tkbletsc/Prusa3/printed_parts/output/Z_-Half_Coupler_v2.stl

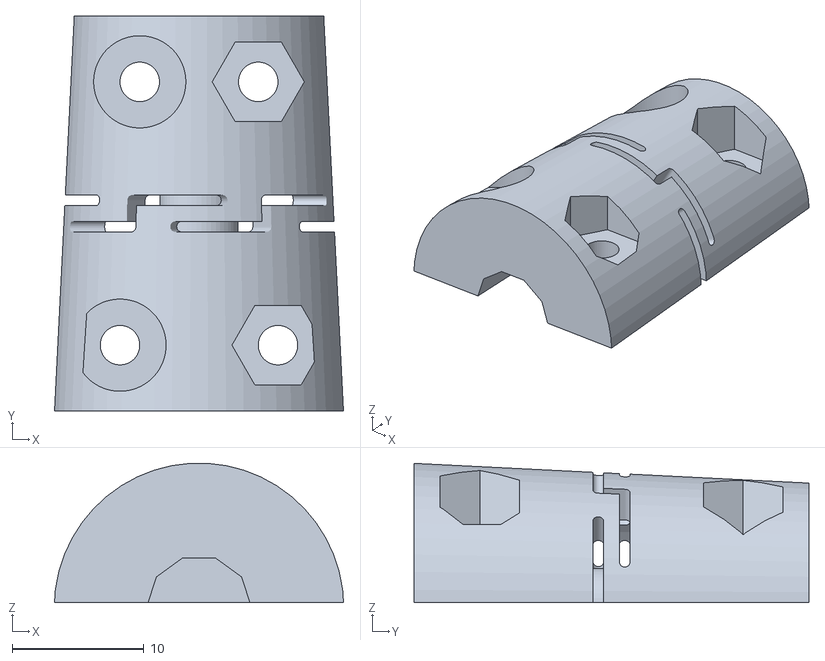
[picture p31: CAD file, 2015-11-13]
printed_parts/output/Z_-Half_Coupler_v2.stl
21.9 x 30.0 x 10.6
