tkbletsc/Prusa3/printed_parts/output/extras/foldingclamp.stl

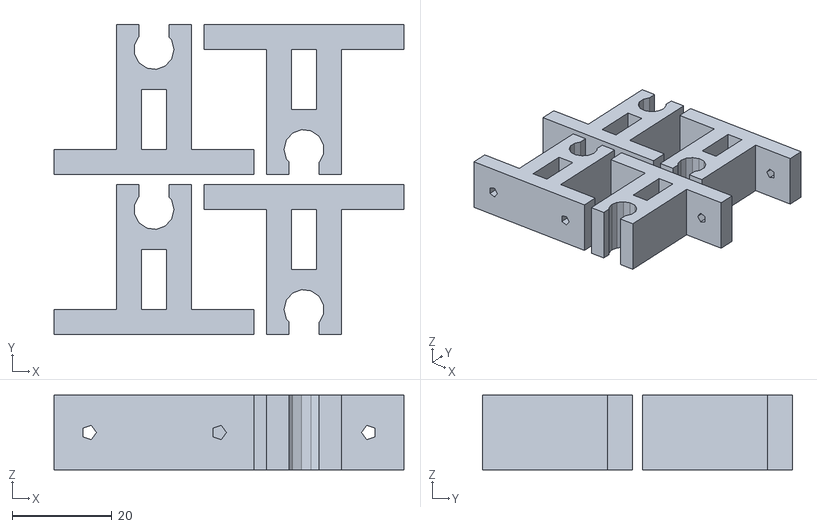
[picture p32: CAD file, 2015-11-13]
printed_parts/output/extras/foldingclamp.stl
70.0 x 62.0 x 15.0
