tkbletsc/Prusa3/printed_parts/output/Pulley_T-MXL-XL-HTD-GT2_N-tooth.stl

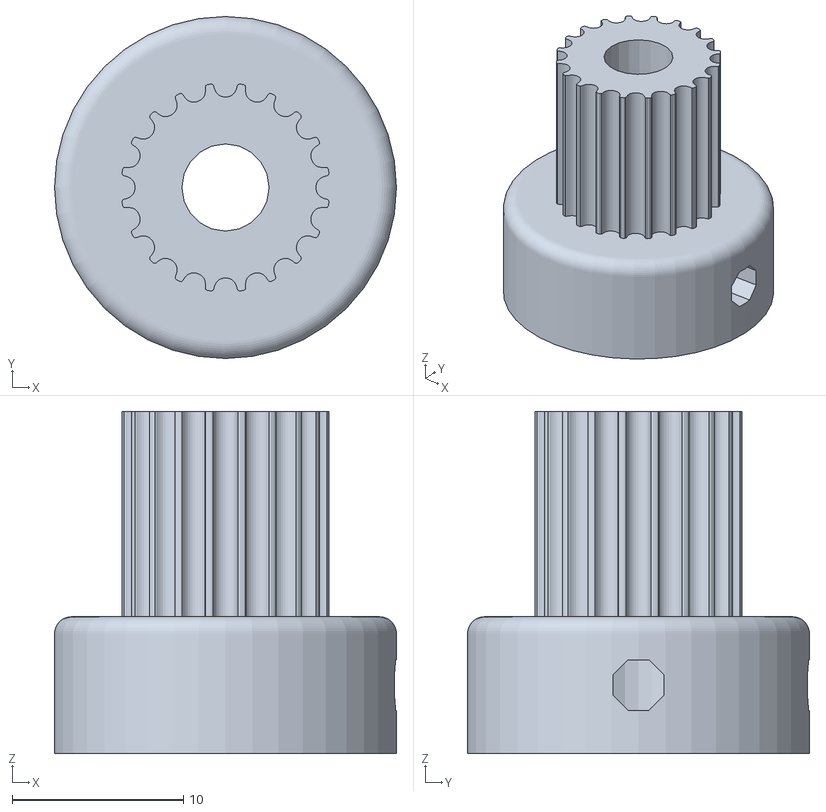
[picture p33: CAD file, 2015-11-13]
printed_parts/output/Pulley_T-MXL-XL-HTD-GT2_N-tooth.stl
20.0 x 20.0 x 20.0
