tkbletsc/Prusa3/printed_parts/output/extras/endstop-holder-extra.stl

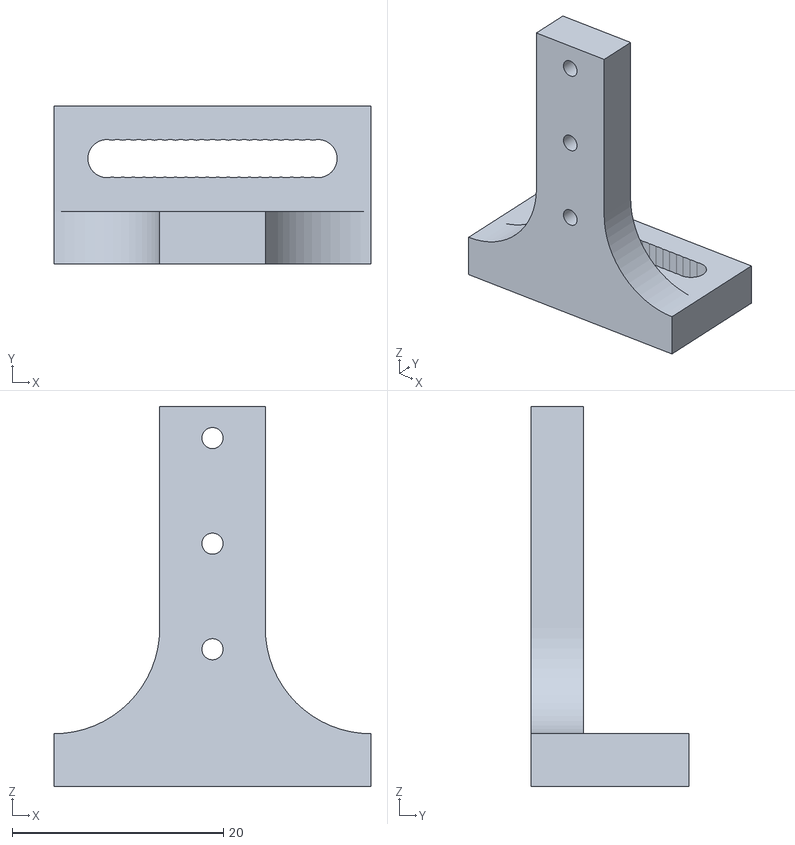
[picture p34: CAD file, 2015-11-13]
printed_parts/output/extras/endstop-holder-extra.stl
30.0 x 15.0 x 36.0
