tkbletsc/Prusa3/printed_parts/output/z-axis.stl

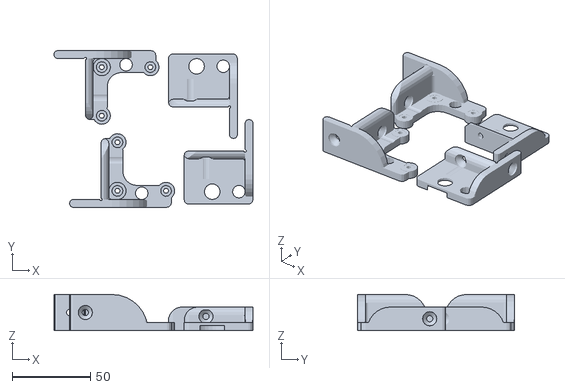
[picture p35: CAD file, 2015-11-13]
printed_parts/output/z-axis.stl
127.0 x 100.0 x 23.0
