tkbletsc/Prusa3/printed_parts/output/extras/gregs-wade-v3.stl

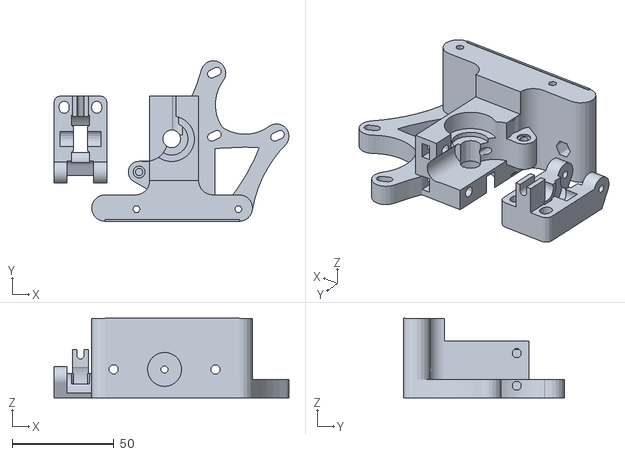
[picture p36: CAD file, 2015-11-13]
printed_parts/output/extras/gregs-wade-v3.stl
115.4 x 78.9 x 39.2
