tkbletsc/Prusa3/printed_parts/output/x-carriage.stl

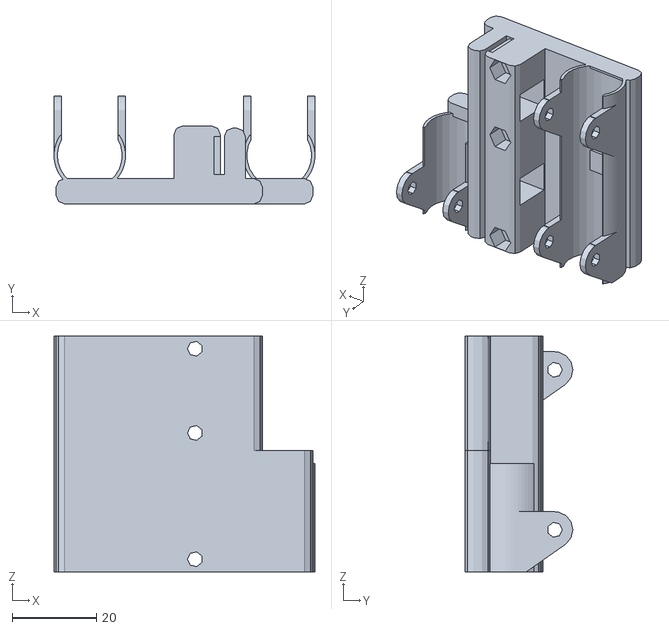
[picture p37: CAD file, 2015-11-13]
printed_parts/output/x-carriage.stl
62.0 x 25.6 x 56.0
