tkbletsc/Prusa3/printed_parts/output/bushing.stl

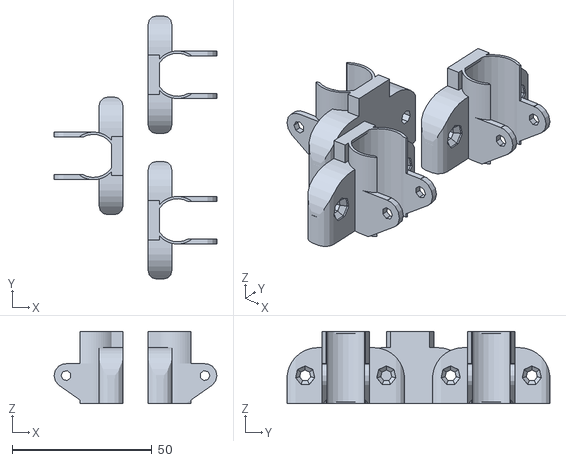
[picture p38: CAD file, 2015-11-13]
printed_parts/output/bushing.stl
58.2 x 94.0 x 25.8
