tkbletsc/Prusa3/printed_parts/output/extras/tube_clamp.stl

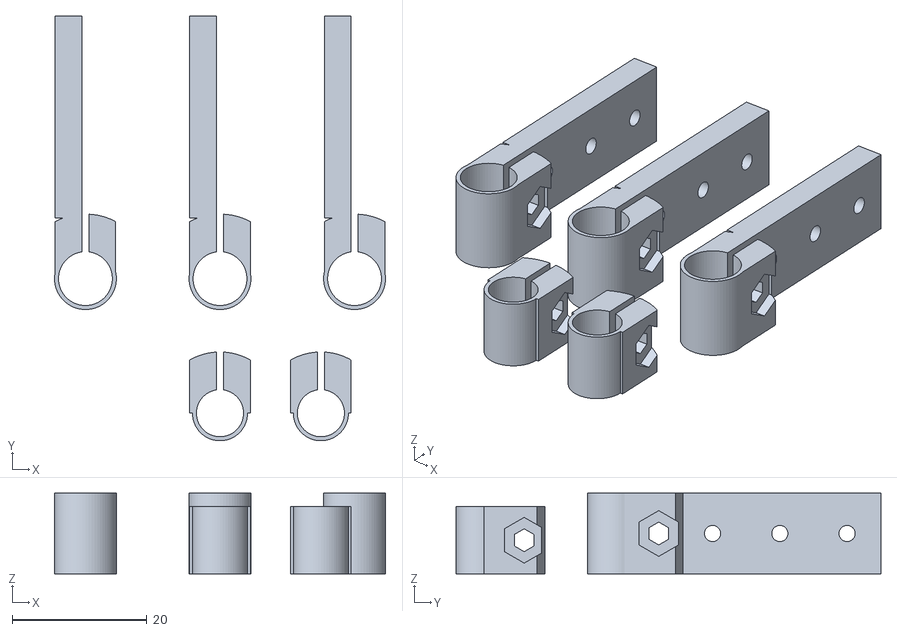
[picture p39: CAD file, 2015-11-13]
printed_parts/output/extras/tube_clamp.stl
49.2 x 63.1 x 12.0
