tkbletsc/Prusa3/printed_parts/output/y-axis-corner.stl

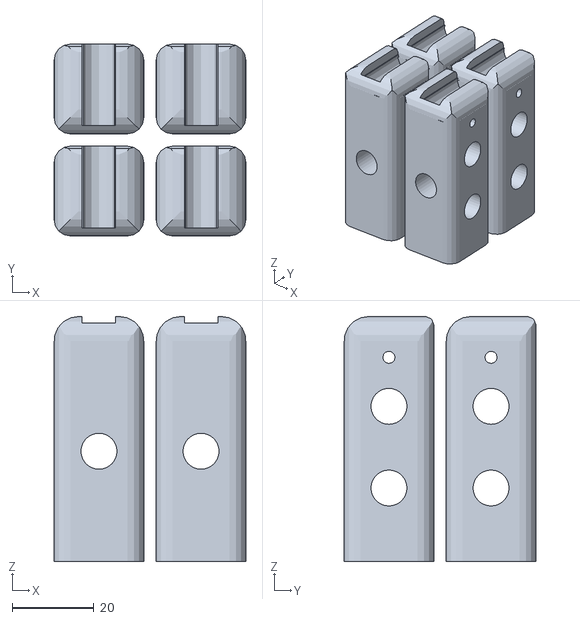
[picture p40: CAD file, 2015-11-13]
printed_parts/output/y-axis-corner.stl
47.0 x 47.0 x 60.0
