tkbletsc/Prusa3/printed_parts/output/spring.stl

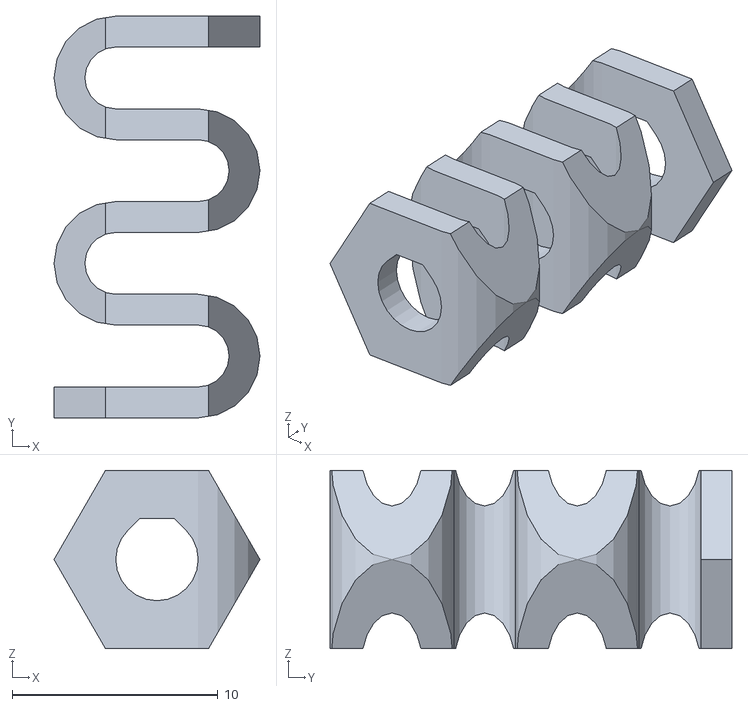
[picture p41: CAD file, 2015-11-13]
printed_parts/output/spring.stl
10.0 x 19.5 x 8.66
